hacker-fab/phoenix/scripts/examples/test_thermocouple/test_thermocouple.ino

#include <Adafruit_MAX31856.h>

// for arduino
// Adafruit_MAX31856 maxthermo = Adafruit_MAX31856(10);

// for esp32 s3 devkitM
Adafruit_MAX31856 maxthermo = Adafruit_MAX31856(34, 35, 37, 36);

void setup() {
  Serial.begin(115200);
  while (!Serial) delay(10);
  Serial.println("MAX31856 thermocouple test");

  if (!maxthermo.begin()) {
    Serial.println("Could not initialize thermocouple.");
    while (1) delay(10);
  }
  
  // Set to K-type thermocouple
  maxthermo.setThermocoupleType(MAX31856_TCTYPE_K);
  Serial.print("Thermocouple type: ");
  switch (maxthermo.getThermocoupleType()) {
    case MAX31856_TCTYPE_K: Serial.println("K Type"); break;
    default: Serial.println("Unknown Type"); break;
  }
}

void loop() {
  // Read temperature
  Serial.print("Cold Junction Temp: ");
  Serial.println(maxthermo.readCJTemperature());
  
  Serial.print("Thermocouple Temp: ");
  Serial.println(maxthermo.readThermocoupleTemperature());
  
  // Check for any faults
  uint8_t fault = maxthermo.readFault();
  if (fault) {
    if (fault & MAX31856_FAULT_CJRANGE) Serial.println("Cold Junction Range Fault");
    if (fault & MAX31856_FAULT_TCRANGE) Serial.println("Thermocouple Range Fault");
    if (fault & MAX31856_FAULT_CJHIGH)  Serial.println("Cold Junction High Fault");
    if (fault & MAX31856_FAULT_CJLOW)   Serial.println("Cold Junction Low Fault");
    if (fault & MAX31856_FAULT_TCHIGH)  Serial.println("Thermocouple High Fault");
    if (fault & MAX31856_FAULT_TCLOW)   Serial.println("Thermocouple Low Fault");
    if (fault & MAX31856_FAULT_OVUV)    Serial.println("Over/Under Voltage Fault");
    if (fault & MAX31856_FAULT_OPEN)    Serial.println("Thermocouple Open Fault");
  }
  
  delay(1000);
}
