hacker-fab/phoenix/scripts/lcd.py

from machine import I2C, Pin
import time
# from enum import Enum

LCD_RESET = 14

I2C_ADDR = 60
CONTROL = 0x00
DATA = 0x00
LINE2 = 0xC0

# class CtrlContinue(Enum):
#     LAST_CTRL = 0
#     MORE_CTRL = 1

# class CtrlType(Enum):
#     INSTRUCTION = 0
#     DATA = 1

class ControlByte():
    def __init__(self, co, rs):
        self.co = co 
        self.rs = rs
    def to_byte(self):
        return (self.co << 7) | (self.rs << 6)


lcd_reset = Pin(LCD_RESET, Pin.OUT)

lcd_reset.value(0)
time.sleep(0.005)
lcd_reset.value(1)

i2c = I2C(0, scl=Pin(13), sda=Pin(12), freq=250_000)

# scan
print(i2c.scan())

# def write_data(data):
#     stuff = bytearray([my_ctrl, data])
#     print(stuff)
#     i2c.writeto(I2C_ADDR, stuff)

# write data
my_ctrl = ControlByte(co=1, rs=1)

text = "HELLO"
data = text.encode('ascii')[:20]
print("type(data)", type(data))
sequence = bytearray([my_ctrl.to_byte()]) + data
i2c.writeto(I2C_ADDR, sequence)

print("write done")
